obelenitsa-cmd/kawa_monitor/kawa_monitor_1.47/DotDigital12.h

const uint8_t DotDigital12Bitmaps[] PROGMEM = {
    0x00, 0x00, 0x00, 0x00, 0x00, 0x00, 0x00, 0x00, 0x00, 0x00, 0x00, 0x00,
    0x00, 0x00, 0x00, 0x00, 0x00, 0x00, 0x00, 0x00, 0x00, 0x00, 0x00, 0x00,
    0x00, 0x00, 0x00, 0x00, 0x00, 0x00, 0x00, 0x00, 0x00, 0x00, 0x00, 0x00,
    0x00, 0x00, 0x00, 0x00, 0x00, 0x00, 0x00, 0x00, 0x00, 0x00, 0x00, 0x00,
    0x00, 0x00, 0x00, 0x00, 0x00, 0x00, 0x00, 0x00, 0x00, 0x00, 0x00, 0x00,
    0x00, 0x00, 0x00, 0x00, 0x00, 0x00, 0x00, 0x00, 0x00, 0x00, 0x00, 0x00,
    0x00, 0x00, 0x00, 0x00, 0x00, 0x00, 0x00, 0x00, 0x00, 0x00, 0x00, 0x00,
    0x00, 0x00, 0x00, 0x00, 0x00, 0x00, 0x00, 0x00, 0x00, 0x00, 0x00, 0x00,
    0x00, 0x00, 0x00, 0x00, 0x00, 0x00, 0x00, 0x00, 0x00, 0x00, 0x00, 0x00,
    0x00, 0x00, 0x00, 0x00, 0x00, 0x00, 0x00, 0x00, 0x00, 0x00, 0x00, 0x00,
    0x00, 0x00, 0x00, 0x00, 0x00, 0x00, 0x00, 0x00, 0x00, 0x00, 0x00, 0x00,
    0x00, 0x00, 0x00, 0x00, 0x00, 0x00, 0x00, 0x00, 0x00, 0x00, 0x00, 0x00,
    0x00, 0x00, 0x00, 0x00, 0x00, 0x00, 0x00, 0x00, 0x00, 0x00, 0x00, 0x00,
    0x05, 0x55, 0x50, 0x00, 0x00, 0x00, 0x05, 0x55, 0x55, 0x00, 0x00, 0x00,
    0x01, 0x40, 0x01, 0x40, 0x00, 0x00, 0x00, 0x50, 0x55, 0x55, 0x00, 0x00,
    0x00, 0x14, 0x55, 0x55, 0x50, 0x00, 0x00, 0x05, 0x14, 0x05, 0x14, 0x00,
    0x00, 0x01, 0x55, 0x55, 0x45, 0x00, 0x00, 0x00, 0x15, 0x55, 0x41, 0x40,
    0x00, 0x00, 0x00, 0x50, 0x00, 0x50, 0x00, 0x00, 0x00, 0x15, 0x55, 0x54,
    0x00, 0x00, 0x00, 0x01, 0x55, 0x54, 0x00, 0x00, 0x00, 0x00, 0x00, 0x00,
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
    {1586, 25, 39, 25, 0, -34},// 0x45 'E'
    {1708, 25, 39, 25, 0, -34},// 0x46 'F'
    {1830, 0, 0, 0, 0, 0},     // 0x47 'G'
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

const GFXfont DotDigital12 PROGMEM = {(uint8_t *)DotDigital12Bitmaps,
		(GFXglyph *)DotDigital12Glyphs, 0x20, 0x7F, 45};

// Approx. 2631 bytes
